Pharias/TAR/doc/tex/titelseite.tex

% Basierend auf https://de.wikibooks.org/wiki/LaTeX/_Eine_Titelseite_erstellen
\begin{titlepage}
	\centering
	\par\vspace{1cm}
	% {\scshape\LARGE it.schule stuttgart \par}
	\vspace{1cm}
	{\scshape\Large Technikerarbeit\par}
	\vspace{1.5cm}
	{\huge\bfseries\scshape Entwicklung einer Smart Home Zentrale auf Basis eines Raspberry PI\par}
	\vspace{2cm}
	{\Large Felix \textsc{Kuschel} \& Manuel \textsc{Starz}\par}
	\vfill
	Betreut durch\par
	~Matthias \textsc{Kohler}

	\vfill

	% Bottom of the page
	{\large \today\par}
\end{titlepage}
