Pharias/TAR/doc/tex/vw_projektrahmen.tex

\subsection{Projektrahmen}\label{vw_projektrahmen}
Das Projekt zur Erstellung einer Smart Home Zentrale wurde von uns, Felix Kuschel und Manuel Starz, durchgeführt. 
Der Projektzeitraum war vom 1. September 2020 bis zum 30. März 2021 angesetzt. 
Es stand zur Umsetzung des Projekts ein unterrichtsfreier Tag pro Woche zur Verfügung.\\
\noindent Des Weiteren wurden die in dem Zeitraum zur Verfügung stehenden Ferien zur Umsetzung des Projekts genutzt. Die Projektbetreuung erfolgt seitens der Schule durch Herr Matthias Kohler. 
Da das Projekt nicht in Zusammenarbeit mit einem Unternehmen durchgeführt wird, gibt es keine weiteren Betreuer. 
Die Materialkosten für die im Projekt genutzte Hardware wurde von uns selbst getragen.
Der im Lastenheft (vgl. Anhang \ref{ah_lastenheft}: \nameref{ah_lastenheft}) erwähnte Verein ,,Smart Home e.V.'' ist ein fiktiver Verein und dient lediglich als Platzhalter.
