Pharias/TAR/doc/tex/zeitplan.tex

\section{Zeitplan}\label{zeitplan}
\begin{figure}[H]
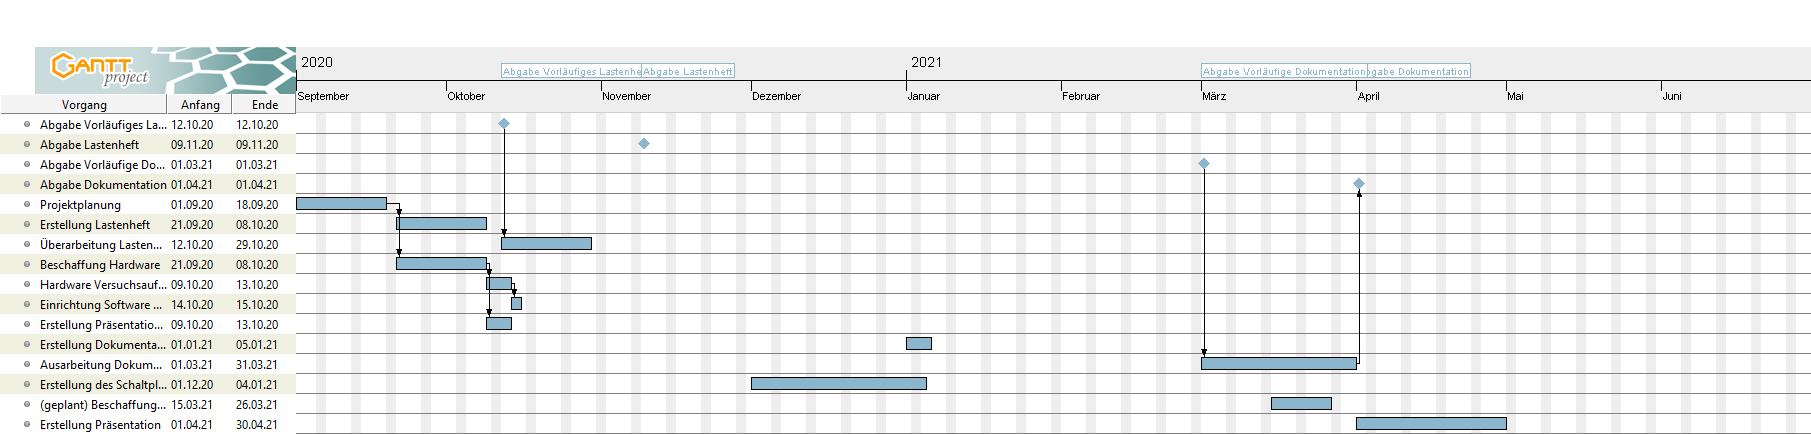
[picture p70: doc/TAR_FKMS_20202021.png]
	
	\caption[Gantt-Diagramm des Projektablaufs]{Gantt-Diagramm des Projektablaufs}
 	\label{fig:gantt-diagramm}
\end{figure}
Um einen besseren Überblick der zu erledigenden Aufgaben zu haben, haben wir mit GanttProject ein Gantt-Diagramm mit den geplanten Aufgaben und Meilensteinen unseres Projekts angelegt (vgl. Abb. \ref{fig:gantt-diagramm}: \nameref{fig:gantt-diagramm}).
Die eigentliche Projektorganisation war als SCRUM Projekt geplant. \\
\noindent Für diesen Zweck haben wir das KANBAN-Board in Microsoft Teams genutzt (vgl. Abb \ref{fig:kanban}: \nameref{fig:kanban}).
Auf Grund dessen haben wir stets einen Überblick über die noch offenen und die bereits erledigten Aufgaben.\\
\begin{figure}[H]
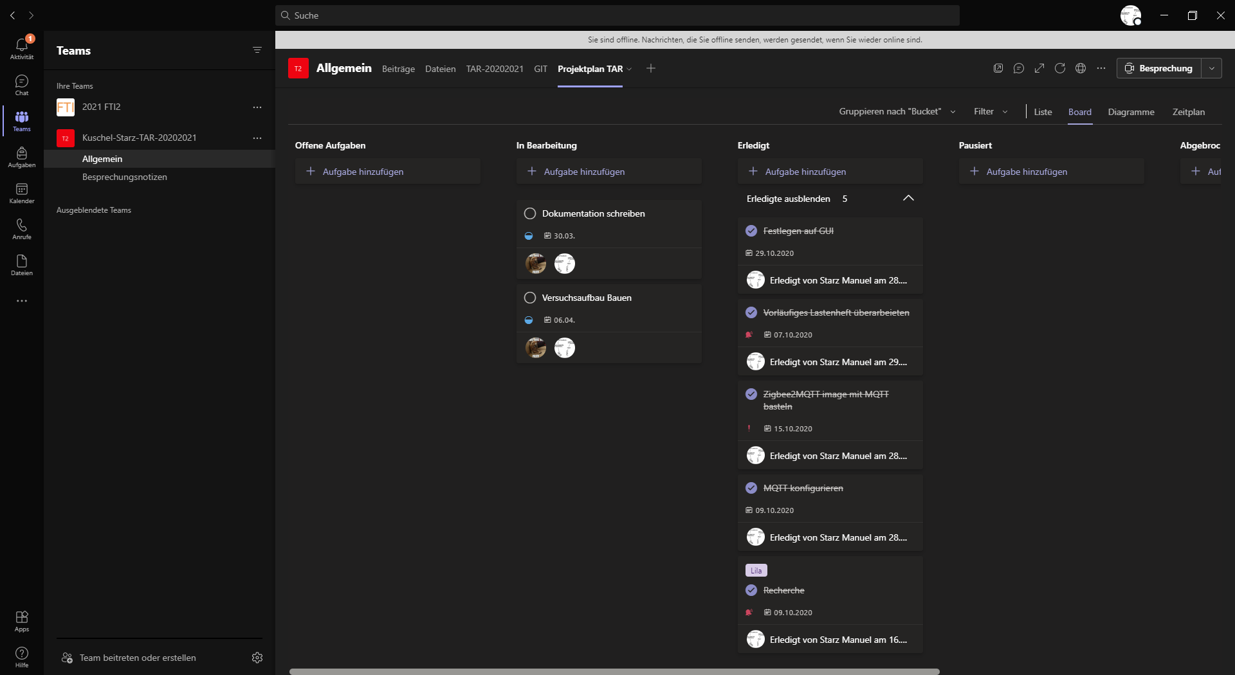
[picture p71: doc/img/teams_kanban.png]
    
    \caption[KANBAN-Board in Microsoft Teams]{KANBAN-Board in Microsoft Teams}
    \label{fig:kanban}
\end{figure}
\noindent Microsoft Teams hat uns auch als Kommunikationsplattform während der Lockdown-Zeiten gedient. 
So konnten wir während der üblichen Besprechungszeiten mit Herr Kohler in Verbindung treten.
\newpage
