Pharias/TAR/doc/tex/zs_anforderungen.tex

\subsection{Anforderungen und gewünschte Features}\label{zs_anforderungen}
Die Anforderungen an das Projekt lauteten wie folgt:
\begin{itemize}
	\item Anbindung von ZigBee-fähigen Endgeräten
	\item Steuerung der angebundenen Endgeräte
	\item Übermittlung der Zustände der angebundenen Geräte an z.B. ein Smartphone
\end{itemize}
Diese Anforderungen lassen sich mit einem Raspberry Pi und einem Zigbee-USB-Stick realisieren. 
Zusätzlich hinaus waren von unserer Seite noch folgende Features geplant:
\begin{itemize}
	\item Ein- und Ausgabe über einen Touch-Bildschirm
	\item Einbindung des Sprachassistenten MyCroft zur Steuerung der verbundenen Endgeräte
\end{itemize}
Zusätzlich haben wir ein Installationsskript und ein Betriebssystem-Image für den Raspberry Pi zu erstellt.\\
\noindent Um das Endprodukt wertiger gestalten zu können,  haben wir zusätzlich ein Gehäuse für die Hardware entworfen.
