Pharias/TAR/doc/tex/zs_konzeption.tex

\subsection{Konzeption}\label{zs_konzeption}
Zu Beginn des Projekts haben wir Nachforschung angestellt und uns bereits vorhandene Open-Source-Lösungen im Bereich Smart Home näher angeschaut.
Dabei sind wir neben dem Smart Mirror GLANCR auch auf die Gesamtlösungen homeassistant.io sowie openHAB gestoßen. 
In Folge dessen haben wir ein Grundkonzept in unserem Lastenheft zusammengefasst und dieses in Absprache mit unserem Betreuungslehrer, Herr Kohler, ausgearbeitet und abgegeben.\par
\noindent Dann konnten wir uns an die Beschaffung der unserer Meinung nach notwendigen Komponenten für das Projekt machen.
