Pharias/TAR/doc/tex/ah_skript.tex

\subsection{Installationsskript}\label{ah_skript}
\inputminted[
frame=lines,
framesep=2mm,
baselinestretch=1.2,
fontsize=\footnotesize,
linenos,
breaklines, 
breakafter=d
]{bash}{misc/shz_install}
\newpage
