Pharias/TAR/doc/tex/erklaerung.tex

\section*{Erklärung}\label{erklaerung}
Hiermit erklären wir, dass die vorliegende Technikerarbeit eine eigenständige Leistung darstellt und nicht auf Basis einer bereits vorhandenen Techniker-, Diplom-, oder ähnlichen Arbeit erstellt wurde.
Verwendete Quellen haben wir vollständig und nachprüfbar aufgeführt.
Bei der Durchführung und Ausarbeitung wurden nur die zulässigen Hilfsmittel verwendet.\\
\noindent Uns ist bewusst, dass bei einem Verstoß gegen diese Erklärung innerhalb der gesetzlichen Einspruchsfristen auch im Nachhinein die Leistungsbewertung aberkannt werden kann.
Damit erlischt die Berechtigung zum Tragen der Berufsbezeichnung ,,staatlich geprüfter Techniker''.\\
\noindent Bedanken möchten wir uns bei Herr Kohler für die Unterstützung und Betreuung bei der Erstellung der Technikerarbeit.
\vspace{2cm}	
\\
\noindent\rule{7cm}{.4pt}\hfill\rule{7cm}{.4pt}\par
\noindent Datum, Ort \hfill Felix Kuschel
\vspace{2cm}	
\\
\noindent\rule{7cm}{.4pt}\hfill\rule{7cm}{.4pt}\par
\noindent Datum, Ort \hfill Manuel Starz
\newpage
