Pharias/TAR/doc/tex/ah_hat.tex

\subsection{Raspberry Pi HAT E-Schema}\label{ah_hat}

\newpage
