Pharias/TAR/doc/tex/vw_aufgabenstellung.tex

\subsection{Aufgabenstellung}\label{vw_aufgabenstellung}
Das Projekt ist aus dem Zusammenschluss der Abschlussarbeitsideen von uns, Felix Kuschel und Manuel Starz, entstanden und wurde in Rücksprache mit dem betreuenden Lehrer entwickelt.\par
\noindent Durch die große Verfügbarkeit von Smart Home Geräten und den zahlreichen Standards der Anbieter entschlossen wir uns, eine einfache und leicht zu replizierende Lösung zu entwickeln, mit der Smart Home Geräte mehrerer Hersteller miteinander verknüpft werden können und so die Notwendigkeit entfällt verschiedene sogenannte Hubs zu müssen.\par
\noindent Das Gerät soll darüber hinaus noch über einen Touchscreen steuerbar sein und die Parameter aller verbundenen Smart Home Geräte anzeigen.
Dies umfasst unter anderem den Status von Leuchtmitteln, die Parameter von Thermostaten, sowie den Zustand von Tür- und Fensterkontakten. 
Die genaue Aufgabenstellung kann dem abgegebenen Lastenheft im Anhang (\ref{ah_lastenheft}: \nameref{ah_lastenheft} entnommen werden.
