Pharias/TAR/doc/tex/vw_einleitung.tex

\subsection{Einleitung}\label{vw_einleitung}
Bei dieser Ausarbeitung handelt es sich um die Abschlussarbeit zur Weiterbildung zum Staatlich geprüften Techniker in der Fachrichtung Informationstechnik.
Diese Arbeit basiert auf dem in den zwei Jahren erlernten Stoffs, sowie selbst erarbeiteten Kenntnissen und dient zur Feststellung des Erreichens des Fortbildungszieles.
