Pharias/TAR/doc/tex/vw_zusatzinformationen.tex

\subsection{Zusatzinformationen}\label{vw_zusatzinformationen}
Die Rohdaten des Projekts wurden der Einfachheit halber in einem GIT-Projekt zusammengefasst.
Dadurch koönnen wir unabhängig voneinander an dem Projekt und der Dokumentation arbeiten.
\noindent Der Link zu dem Projekt lautet:\\
\url{https://github.com/Pharias/TAR}\par
\noindent Ursprünglich war dafür die Verwendung des schulinternen GIT geplant.
Dieses stand zum Zeitpunkt der Erstellung der Dokumentation allerdings nicht zur Verfügung\footnote{War lt. Herr Kohler nicht verfügbar aufgrund von Sicherheitsrisiken}, weshalb GITHub genutzt wurde.
