Pharias/TAR/doc/tex/zielsetzung.tex

\section{Zielsetzung}\label{zielsetzung}
Als Ziel für das Projekt war ein funktionsfähiges Smart Home Hub mit Zigbee-Anbindung auf Basis eines Raspberry Pi 4 geplant. 
Das Smart Home Hub in seiner Grundfunktion soll in der Lage sein, die mit ihm verbundenen Geräte über den Zigbee-Standard anzusteuern.
Zusätzlich sollte die Möglichkeit einer Erweiterung mit einem Sprachassistenten möglich sein.\par
% Konzeption
\input{tex/zs_konzeption}
% Anforderungen und gewünschte Features
\input{tex/zs_anforderungen}
% Erweiterungsmöglichkeiten
\input{tex/zs_erweiterung}
\newpage
