Pharias/TAR/doc/tex/hw_case.tex

\subsection{Gehäuse}\label{hw_case}
% Erster Test
\input{tex/hw_case_ersterTest}
% Modellentwicklung am Objekt
\input{tex/hw_case_modellentwicklung}
% Erstellung des Modells
\input{tex/hw_case_herstellung}
