Pharias/TAR/doc/tex/vw_datenschutz.tex

\subsection{Datenschutzhinweis}\label{vw_datenschutz}
Aus Datenschutzgründen sind lokale IP-Adressen und lokale Domänennamen innerhalb der Dokumentation unkenntlich gemacht.
