Pharias/TAR/doc/img/druck_gehäuse_003.png

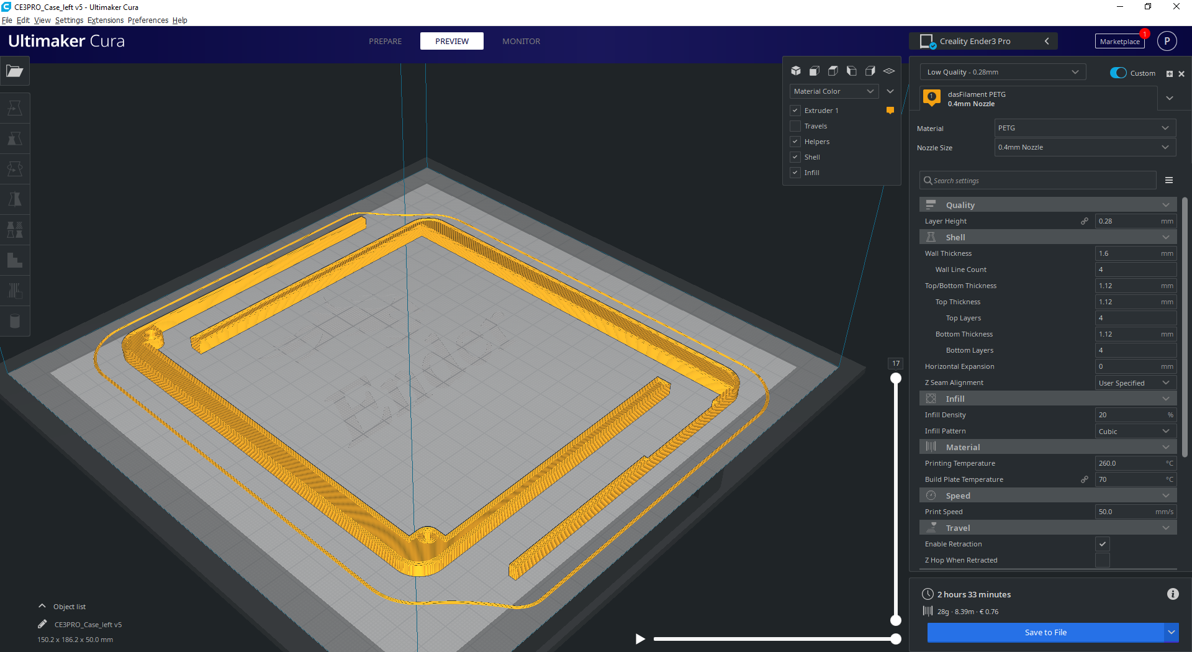
doc/img/druck_gehäuse_003.png
