Pharias/TAR/doc/img/HA10.png

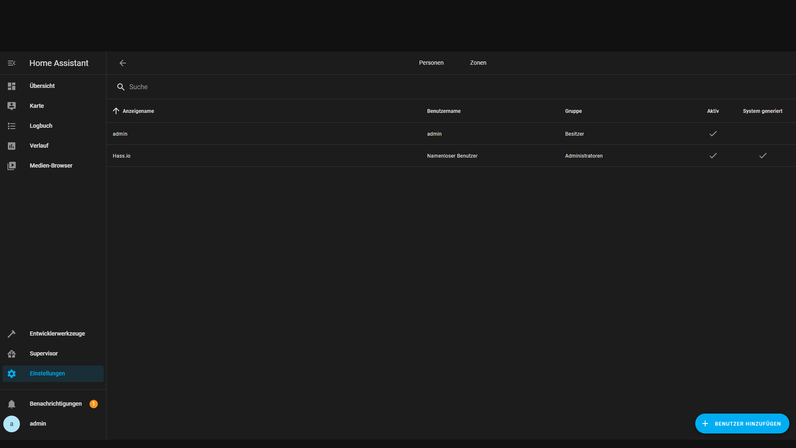
doc/img/HA10.png
