Pharias/TAR/doc/img/HA11.png

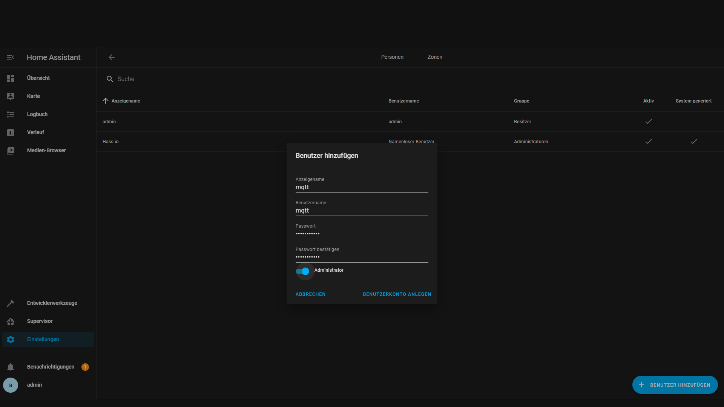
doc/img/HA11.png
