Pharias/TAR/doc/img/HA19.png

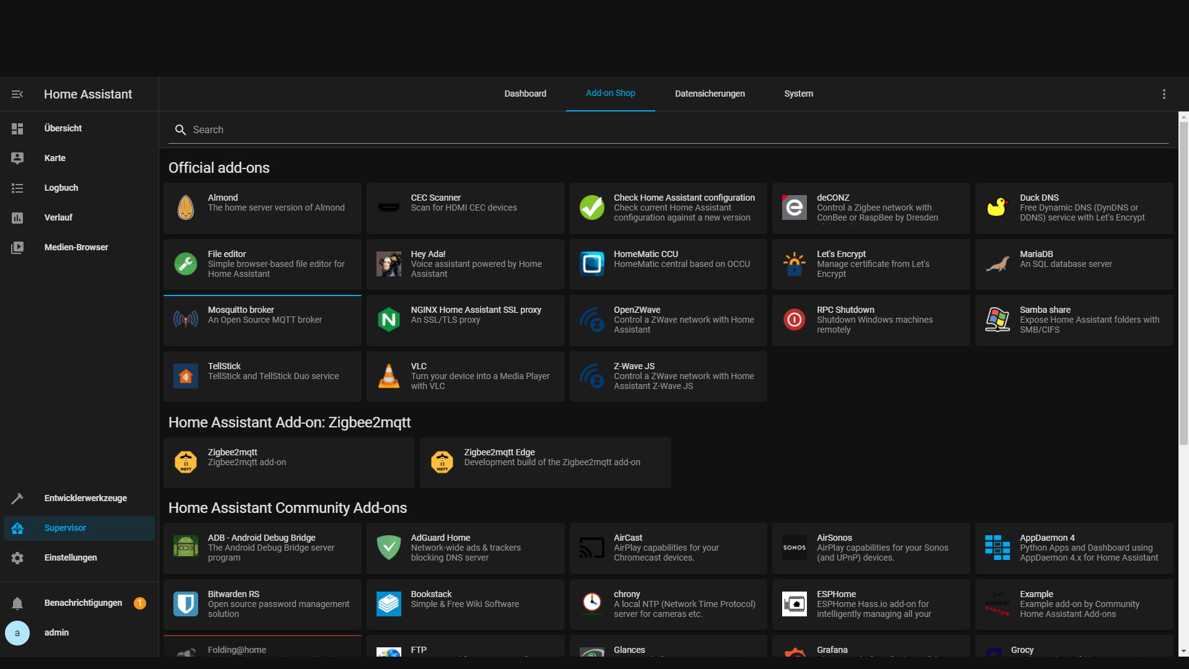
doc/img/HA19.png
