Pharias/TAR/doc/img/placeholder.png

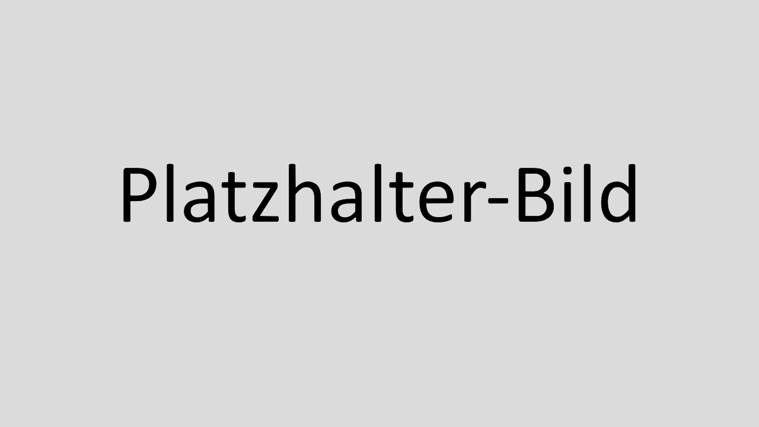
doc/img/placeholder.png
